evanparizot/wordclock/firmware/src/clock.rs

extern crate alloc;
use alloc::boxed::Box;
use cortex_m::prelude::_embedded_hal_blocking_delay_DelayMs;
use ds323x::{ic::DS3231, interface::I2cInterface, DateTimeAccess, Ds323x, Timelike, Rtcc};
use ds323x::Hours::H24;
use hal::{
    gpio::{Alternate, Gpiob, OpenDrain, Output, Pin, PushPull, U},
    i2c::I2c,
    pac::{I2C1, SPI2},
    spi::Spi, delay::Delay,
};
use max7219::{connectors::SpiConnectorSW, MAX7219};

use crate::times::TimeMode;

pub struct Clock {
    pub(crate) display: MAX7219<
        SpiConnectorSW<
            Spi<
                SPI2,
                (
                    Pin<Gpiob, U<13>, Alternate<PushPull, 5>>,
                    Pin<Gpiob, U<14>, Alternate<PushPull, 5>>,
                    Pin<Gpiob, U<15>, Alternate<PushPull, 5>>,
                ),
            >,
            Pin<Gpiob, U<12>, Output<PushPull>>,
        >,
    >,
    pub(crate) clock: Ds323x<
        I2cInterface<
            I2c<
                I2C1,
                (
                    Pin<Gpiob, U<6>, Alternate<OpenDrain, 4>>,
                    Pin<Gpiob, U<7>, Alternate<OpenDrain, 4>>,
                ),
            >,
        >,
        DS3231,
    >,
    pub(crate) mode: Box<dyn TimeMode + Send>,
    pub(crate) last_frame: [[u8; 8]; 4],
}

impl Clock {
    pub fn update_display_time(&mut self) {
        // Get current time, in hours, minutes and seconds
        let (hour, minutes, _seconds) = self.get_time();
        let to_write = self.mode.get_time_arrays(hour, minutes);

        self.last_frame = to_write;

        self.write_time_arrays(&to_write);
    }

    fn write_time_arrays(&mut self, time: &[[u8; 8]; 4]) {
        time.iter().enumerate().for_each(|(i, x)| {
            self.display.write_raw(i, x).unwrap();
        });
    }

    pub fn set_intensity(&mut self, displays: usize, intensity: u8) {
        for d in 0..displays {
            self.display.set_intensity(d, intensity).unwrap();
        }
    }

    pub fn get_time(&mut self) -> (u32, u32, u32){
        self.time()
    }

    pub fn add_minutes(&mut self, amount: u8) {
        let (_, minutes, _) = self.time();
        let to_set = (minutes + u32::from(amount)) % 60;
        self.clock.set_minutes(to_set as u8).unwrap();
    }

    pub fn add_hours(&mut self, amount: u8) {
        let (hours, _, _) = self.time();
        let to_set = (hours + u32::from(amount)) % 24;
        self.clock.set_hours(H24(to_set as u8)).unwrap();
    }

    fn time(&mut self) -> (u32, u32, u32) {
        let datetime = self.clock.datetime().unwrap();
        let hour = datetime.time().hour();
        let minute = datetime.time().minute();
        let seconds = datetime.time().second();

        (hour, minute, seconds)
    }

    pub fn set_heartbeat(&mut self, on: bool) {
        const MODULE: usize = 3;
        const ROW: usize = 7;
        const COL: u8 = 7;

        let bit: u8 = 1 << COL;

        let mut module_rows = self.last_frame[MODULE];
        let base = module_rows[ROW];
        module_rows[ROW] = if on { base | bit } else { base & !bit };

        self.display.write_raw(MODULE, &module_rows).unwrap();
    }

    pub fn apply_time_based_brightness (
        &mut self, night_start: u8, night_end: u8, day: u8, night: u8,
    ) -> u8 {
        let (h, _m, _s) = self.get_time();
        let h = h as u8;

        let in_night = if night_start <= night_end {
            h >= night_start && h < night_end
        } else {
            h >= night_start || h < night_end
        };

        let level = if in_night { night } else { day };

        let module_count = self.last_frame.len();
        self.set_intensity(module_count, level);
        level
    }
}
